01binary/businesscard/dependencies/TS-1088-AR02016/TS-1088-AR02016.step

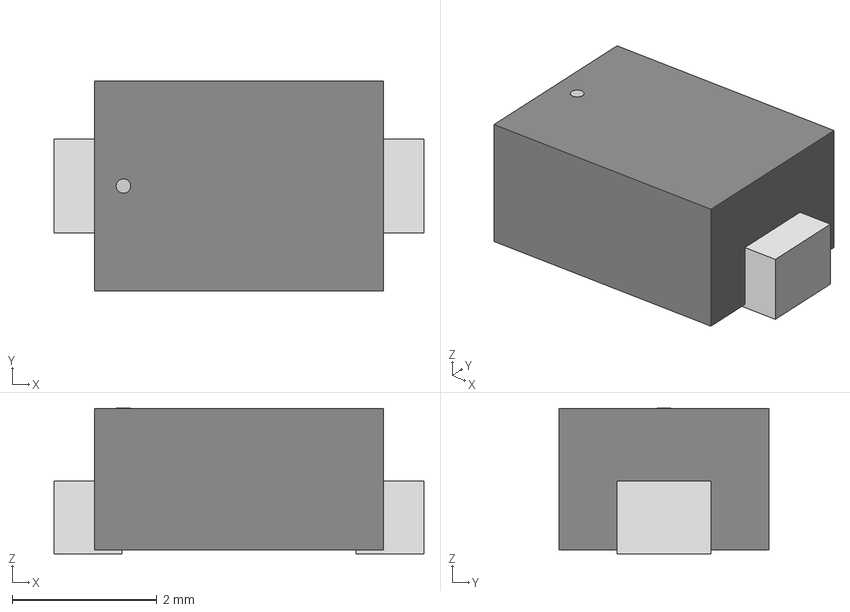
[picture p18: CAD file, 2026-07-01]
dependencies/TS-1088-AR02016/TS-1088-AR02016.step
5.11 x 2.90 x 2.01 mm
