01binary/businesscard/dependencies/UJ20_C_H_G_MSMT_5_P16_TR/UJ20-C-H-G-MSMT-5-P16-TR.step

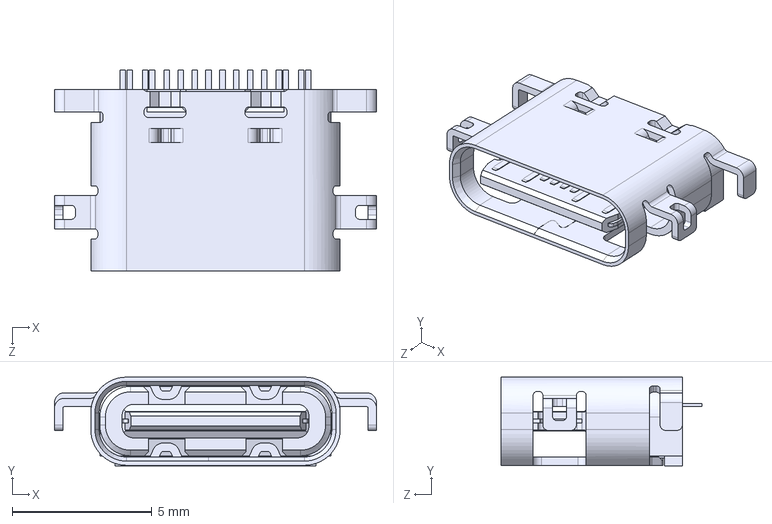
[picture p19: CAD file, 2026-07-01]
dependencies/UJ20_C_H_G_MSMT_5_P16_TR/UJ20-C-H-G-MSMT-5-P16-TR.step
11.5 x 3.18 x 7.20 mm
